artekw/Yaydio-esp32/src/mp3_player.h

#include <Arduino.h>
#include <DYPlayerArduino.h>
#include <HardwareSerial.h>


class YMP3Player {
   public:
    YMP3Player(byte rxPin, byte txPin) : _rxPin(rxPin), _txPin(txPin), _player(&Serial1) {}

    bool begin() {
        Serial1.begin(9600, SERIAL_8N1, _rxPin, _txPin);
        _player.begin();
        _player.setVolume(MP3_INITIAL_VOLUME);
        _player.setCycleMode(DY::play_mode_t::RepeatDir);
        _player.setEq(MP3_EQ_MODE);
        _player.stop();

        return !(_player.checkPlayState() == DY::play_state_t::Fail);
    }

    void playAlbum(uint16_t album) {
        char path[14];
        sprintf(path, "/%04d/001.mp3", album);

        _player.stop();
        _player.playSpecifiedDevicePath(DY::device_t::Sd, path);
        _isPlaying = true;
        delay(1000);
        _firstTrackInAlbum = _player.getFirstInDir();
    }

    void togglePlayback() {
        _isPlaying = !_isPlaying;

        if (_isPlaying) {
            _player.play();
        } else {
            _player.pause();
        }
    }

    void increaseVolume() { _player.volumeIncrease(); }

    void decreaseVolume() { _player.volumeDecrease(); }

    void next() {
        _player.next();
        _isPlaying = true;
    }

    void previous() {
        _player.previous();
        _isPlaying = true;
    }

    void stop() {
        _player.stop();
        _isPlaying = false;
    }

    bool isPlaying() { return _isPlaying; }

    bool toggleRandom() {
        _isRandomOn = !_isRandomOn;
        _player.setCycleMode(_isRandomOn ? DY::play_mode_t::RandomDir : DY::play_mode_t::RepeatDir);
        return _isRandomOn;
    }

    uint16_t currentTrack() { return _player.getPlayingSound() - _firstTrackInAlbum + 1; }

   private:
    byte _rxPin;
    byte _txPin;
    DY::Player _player;
    uint16_t _firstTrackInAlbum;
    bool _isPlaying = false;
    bool _isRandomOn = false;
};
